FreeRangeLobster/Firefly/Pics/IMG_20201202_141513.jpg

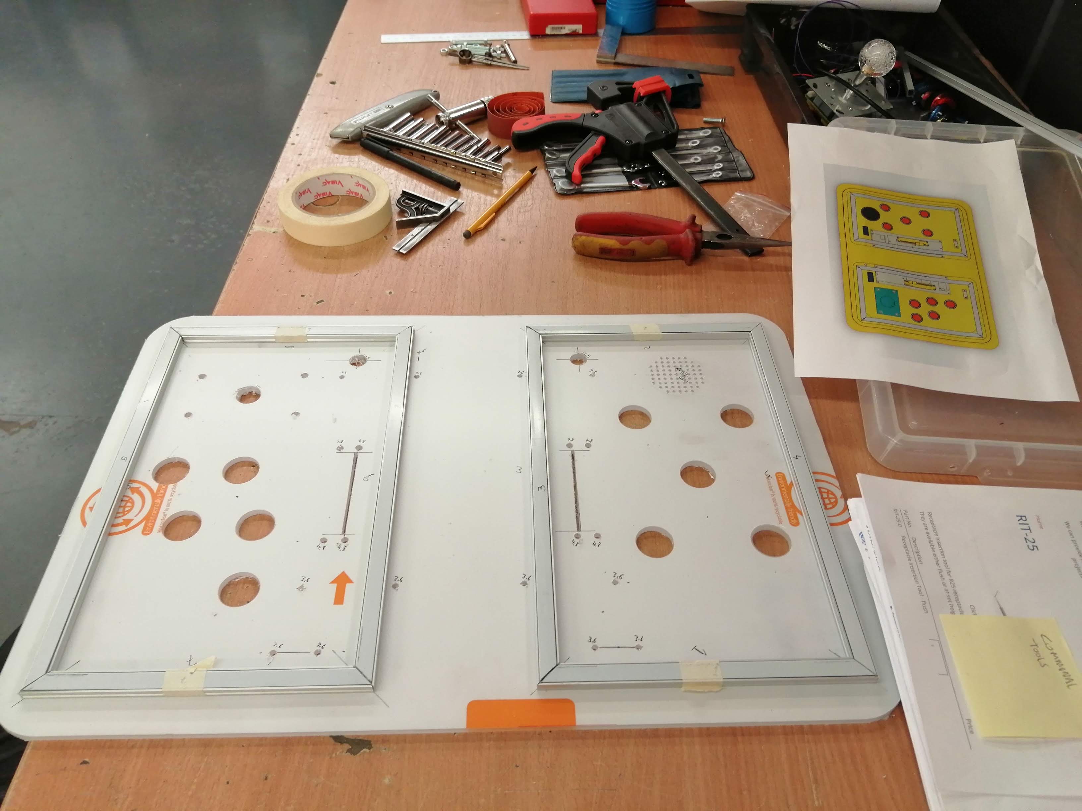
Pics/IMG_20201202_141513.jpg
