FreeRangeLobster/Firefly/Pics/IMG_20201202_171936.jpg

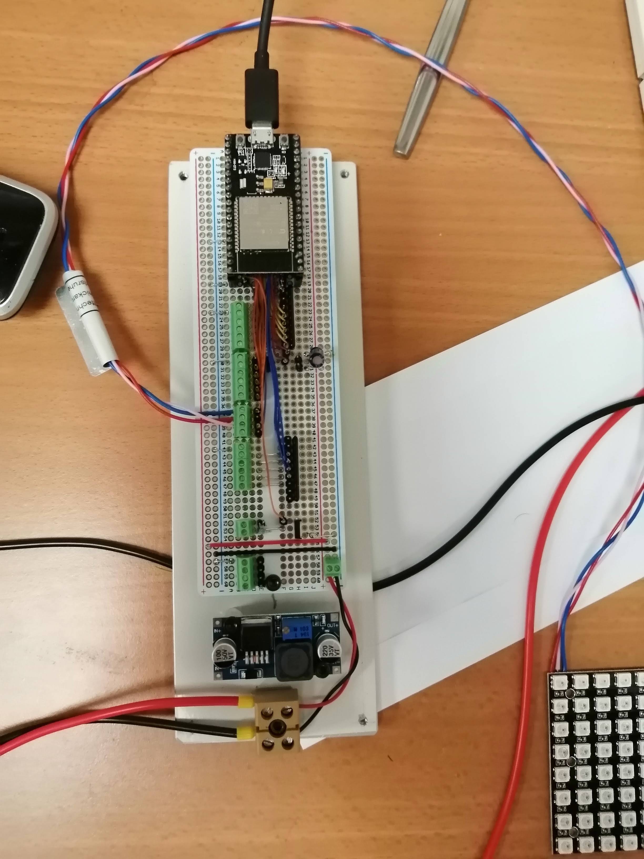
Pics/IMG_20201202_171936.jpg
