FreeRangeLobster/Firefly/Pics/Top.PNG

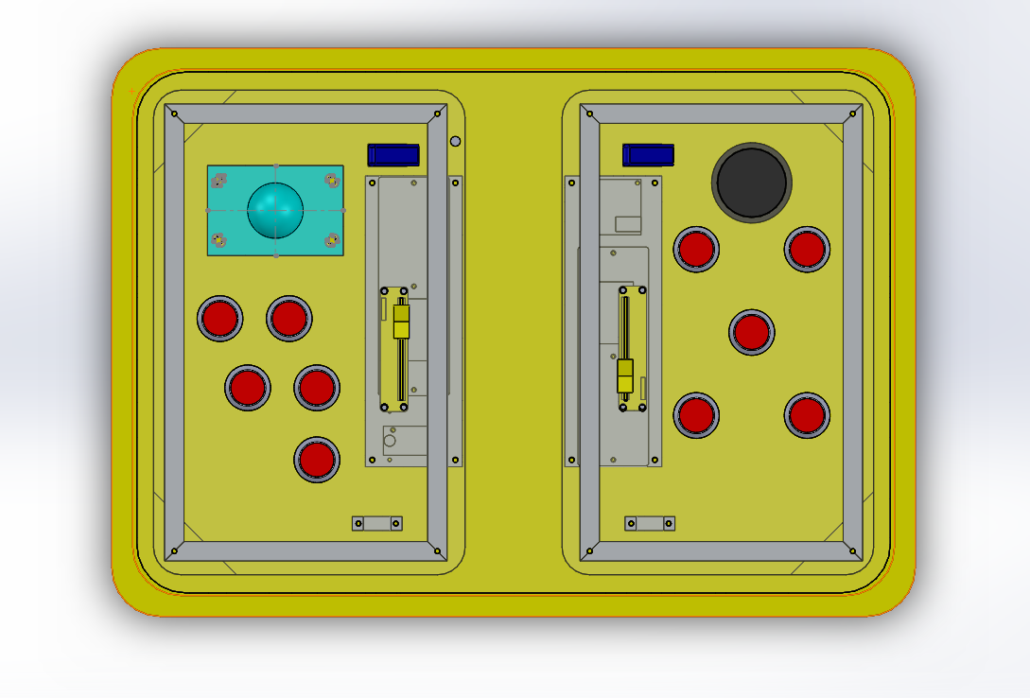
Pics/Top.PNG
