FreeRangeLobster/Firefly/TheMechanics/PCB.SLDPRT

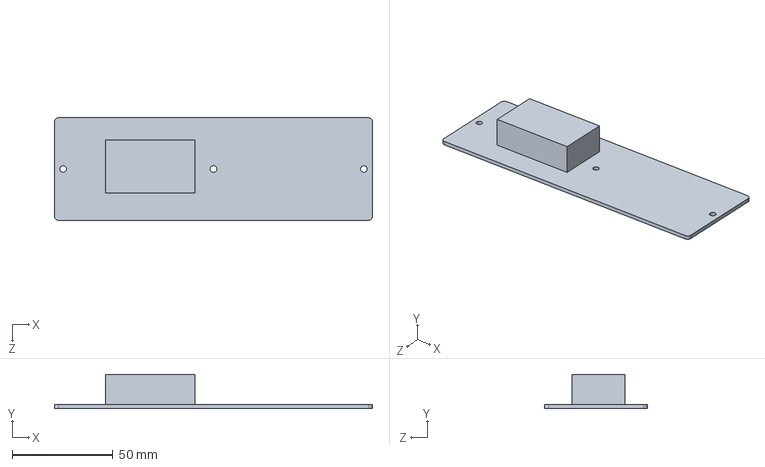
[picture p26: CAD file, 2020-11-17]
TheMechanics/PCB.SLDPRT
158.0 x 17.0 x 51.0 mm
