FreeRangeLobster/Firefly/TheMechanics/PSU.SLDPRT

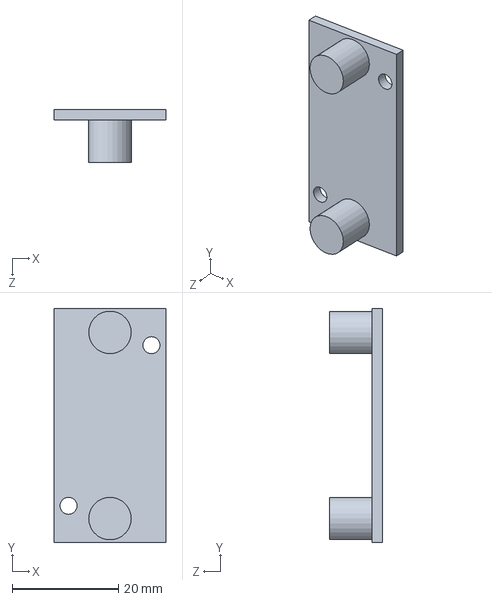
[picture p27: CAD file, 2020-11-17]
TheMechanics/PSU.SLDPRT
21.0 x 44.0 x 10.0 mm
