FreeRangeLobster/Firefly/TheMechanics/Veroboard.SLDPRT

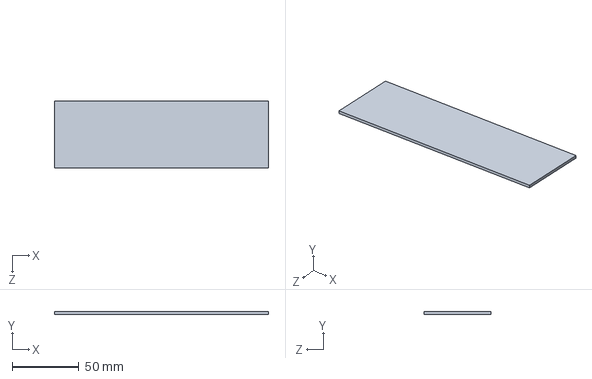
[picture p28: CAD file, 2020-11-16]
TheMechanics/Veroboard.SLDPRT
160.0 x 2.00 x 50.0 mm
