FreeRangeLobster/Firefly/TheMechanics/MP3.SLDPRT

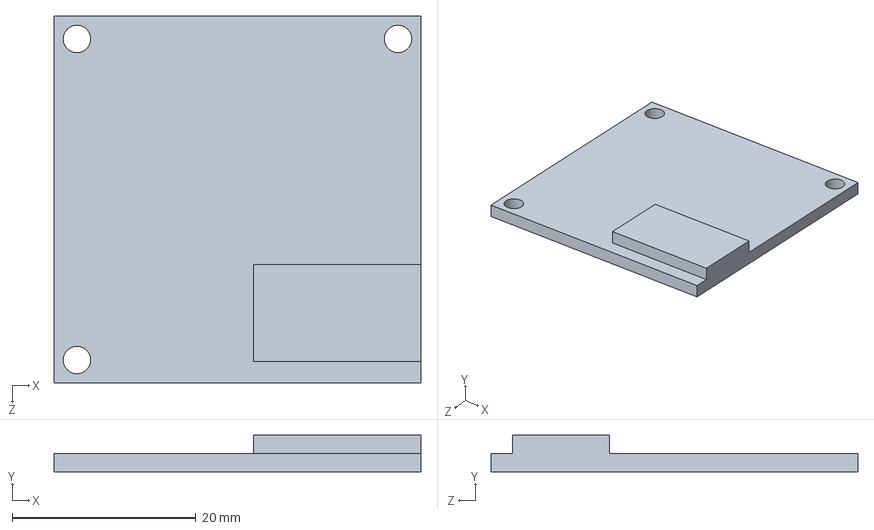
[picture p29: CAD file, 2020-11-16]
TheMechanics/MP3.SLDPRT
40.0 x 4.00 x 40.0 mm
